kiryam/warm_floor/firmware/warm_floor_logic/src/cbuff.c

#include "cbuff.h"
#include "stdbool.h"


int circular_buf_reset(CircualBuffer * cbuf){
    int r = -1;

    if(cbuf) {
        cbuf->head = 0;
        cbuf->tail = 0;
        r = 0;
    }
    return r;
}

bool circular_buf_empty(CircualBuffer cbuf){
    // We define empty as head == tail
    return (cbuf.head == cbuf.tail);
}

bool circular_buf_full(CircualBuffer cbuf){
    // We determine "full" case by head being one position behind the tail
    // Note that this means we are wasting one space in the buffer!
    // Instead, you could have an "empty" flag and determine buffer full that way
    return ((cbuf.head + 1) % cbuf.size) == cbuf.tail;
}


int circular_buf_put(CircualBuffer * cbuf, uint8_t data){
    int r = -1;

    if(cbuf){
        cbuf->buffer[cbuf->head] = data;
        cbuf->head = (cbuf->head + 1) % cbuf->size;

        if(cbuf->head == cbuf->tail) {
            cbuf->tail = (cbuf->tail + 1) % cbuf->size;
        }

        r = 0;
    }

    return r;
}

int circular_buf_get(CircualBuffer * cbuf, uint8_t * data){
    int r = -1;

    if(cbuf && data && !circular_buf_empty(*cbuf)) {
        *data = cbuf->buffer[cbuf->tail];
        cbuf->tail = (cbuf->tail + 1) % cbuf->size;

        r = 0;
    }

    return r;
}
