kiryam/warm_floor/firmware/warm_floor_logic/src/drivers/DS18B20.h

#pragma once

#include "stdint.h"

#define MAX_SENSORS    3

uint8_t ds18b20_start_convert(void);
uint8_t ds18b20_init(void);
float ds18b20_get_temp(uint8_t dev_id);

float ds18b20_tconvert(uint8_t LSB, uint8_t MSB);
